en7angled/CardanoTicker/m1/dashboard_mockups/network_dashboard/network_stats.jpeg

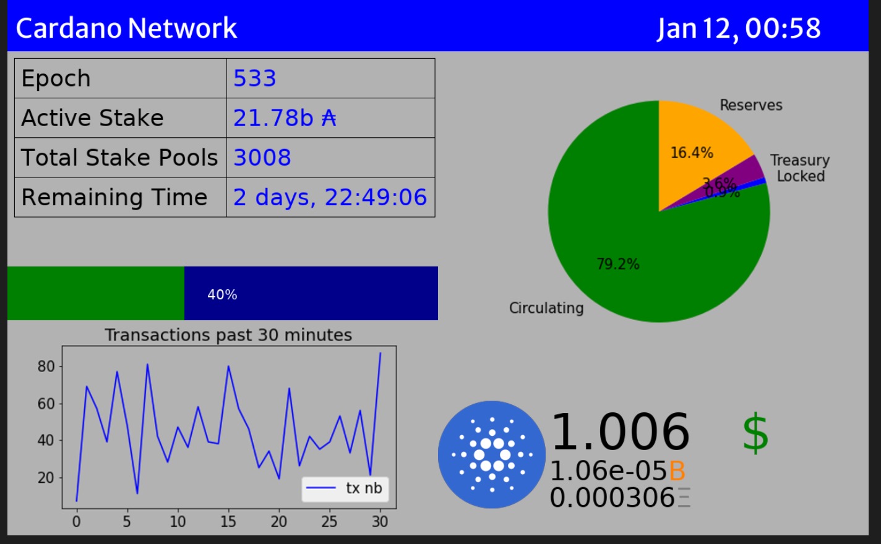
m1/dashboard_mockups/network_dashboard/network_stats.jpeg
