en7angled/CardanoTicker/m1/dashboard_mockups/network_dashboard/network_stats_dark.png

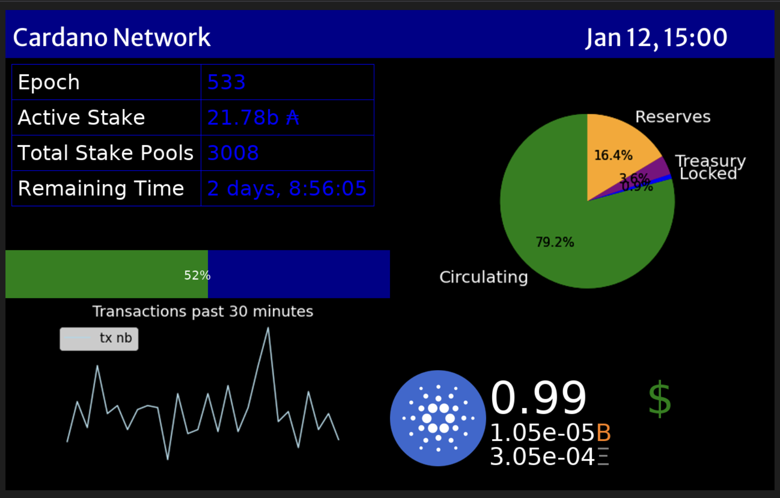
m1/dashboard_mockups/network_dashboard/network_stats_dark.png
