en7angled/CardanoTicker/m1/dashboard_mockups/pool_dashboard/pool_complex.jpeg

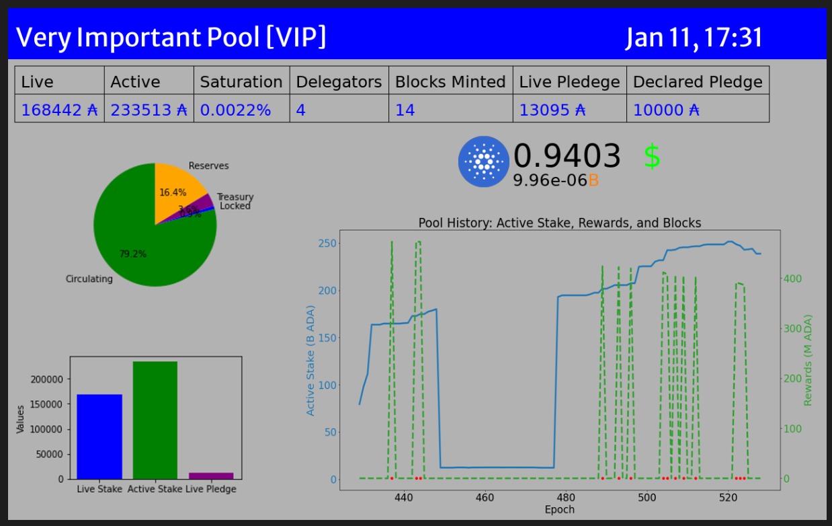
m1/dashboard_mockups/pool_dashboard/pool_complex.jpeg
