en7angled/CardanoTicker/src/cardano_ticker/data/frame.bmp

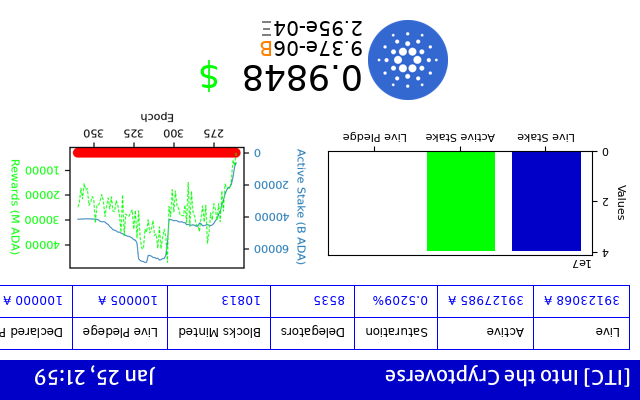
src/cardano_ticker/data/frame.bmp
