en7angled/CardanoTicker/src/cardano_ticker/resources/case_models/waveshare_4.01/img.jpeg

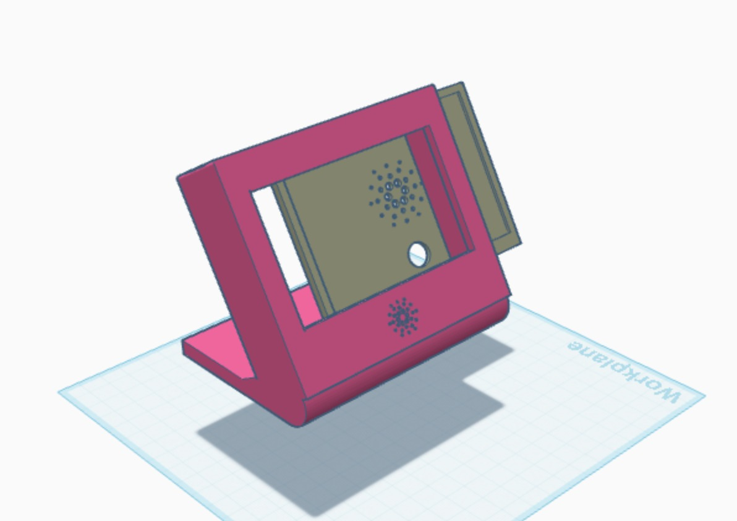
src/cardano_ticker/resources/case_models/waveshare_4.01/img.jpeg
