en7angled/CardanoTicker/src/displayers/esp32/displayer/displayer_config.h

#ifndef DISPLAYER_CONFIG_H
#define DISPLAYER_CONFIG_H

#define WIFI_SSID "AndreiG"
#define WIFI_PASSWORD "123Andrei"
#define SERVER_URL "http://lcdframe.local:5335/latest-image"

#endif // DISPLAYER_CONFIG_H
